DesignSparkRS/ESDK/hardware/PEA/DSPCB/ESDK-PEA (PCB - Plot Report).htm

## Plot Report

Report Written: | Tuesday, October 19, 2021
Project Path: | C:\Users\Callum\Google Drive\ABOPShared\Customer\RS\Projects\Team\Air Quality Sensor Dev Platform\Hardware\PMOD Transition Board\DSPCB Project\PMOD Transition Board.prj
Design Path: | C:\Users\Callum\Google Drive\ABOPShared\Customer\RS\Projects\Team\Air Quality Sensor Dev Platform\Hardware\PMOD Transition Board\DSPCB Project\ESDK-PEA.pcb
Design Title:
Created: | 10/08/2021 11:33:29
Last Saved: | 04/10/2021 16:04:47
Editing Time: | 2646 min
Units: | mm (precision 3)

## Device Settings

### Gerber Settings

Leading zero suppression.
G01 assumed throughout.
Line termination <*> .
3.5 format absolute inches.
Format commands defined in Gerber file.
Aperture table defined in Gerber file.
Hardware arcs allowed.

### Drill Settings

Excellon Format 2
Format 3.5 absolute in mm.
Zero suppression Leading

## Plots Output

### Gerber Output

C:\Users\Callum\Google Drive\ABOPShared\Customer\RS\Projects\Team\Air Quality Sensor Dev Platform\Hardware\PMOD Transition Board\DSPCB Project\Outputs\ESDK-PEA - Top Silkscreen.gbr

Layers:
Top Silkscreen

D-Code | Shape (thou)
D106 | Round 5.00
D107 | Round 3.94
D108 | Round 7.87
D109 | Round 10.00

### Gerber Output

C:\Users\Callum\Google Drive\ABOPShared\Customer\RS\Projects\Team\Air Quality Sensor Dev Platform\Hardware\PMOD Transition Board\DSPCB Project\Outputs\ESDK-PEA - Top Copper.gbr

Layers:
Top Copper

D-Code | Shape (thou)
D106 | Round 5.00
D108 | Round 7.87
D109 | Round 10.00
D110 | Round 25.00
D111 | Round 9.84
D112 | Round 35.43
D113 | Round 19.69
D114 | Round 15.00
D115 | Round 61.02
D116 | Rectangle 31.50 X 51.18 Rotation 90
D117 | Rectangle 82.68 X 118.11 Rotation 90
D118 | Round 55.12
D119 | Rectangle 39.37 X 42.91
D120 | Rectangle 39.37 X 42.91 Rotation 90

### Gerber Output

C:\Users\Callum\Google Drive\ABOPShared\Customer\RS\Projects\Team\Air Quality Sensor Dev Platform\Hardware\PMOD Transition Board\DSPCB Project\Outputs\ESDK-PEA - Top Copper (Resist).gbr

Layers:
Top Copper

D-Code | Shape (thou)
D12 | Round 135.98
D13 | Round 71.02
D17 | Rectangle 49.37 X 52.91 Rotation 90
D18 | Rectangle 49.37 X 52.91
D26 | Rectangle 41.50 X 61.18 Rotation 90
D27 | Rectangle 92.68 X 128.11 Rotation 90
D121 | Round 65.12

### Gerber Output

C:\Users\Callum\Google Drive\ABOPShared\Customer\RS\Projects\Team\Air Quality Sensor Dev Platform\Hardware\PMOD Transition Board\DSPCB Project\Outputs\ESDK-PEA - Top Paste.gbr

Layers:
Top Paste

D-Code | Shape (thou)
D83 | Rectangle 35.43 X 38.98 Rotation 90
D84 | Rectangle 35.43 X 38.98
D94 | Rectangle 28.35 X 48.03 Rotation 90
D95 | Rectangle 74.41 X 109.84 Rotation 90

### Gerber Output

C:\Users\Callum\Google Drive\ABOPShared\Customer\RS\Projects\Team\Air Quality Sensor Dev Platform\Hardware\PMOD Transition Board\DSPCB Project\Outputs\ESDK-PEA - Bottom Copper.gbr

Layers:
Bottom Copper

D-Code | Shape (thou)
D106 | Round 5.00
D108 | Round 7.87
D109 | Round 10.00
D110 | Round 25.00
D111 | Round 9.84
D112 | Round 35.43
D115 | Round 61.02
D118 | Round 55.12

### Gerber Output

C:\Users\Callum\Google Drive\ABOPShared\Customer\RS\Projects\Team\Air Quality Sensor Dev Platform\Hardware\PMOD Transition Board\DSPCB Project\Outputs\ESDK-PEA - Bottom Resist.gbr

Layers:
Bottom Resist

D-Code | Shape (thou)
D122 | Round 41.43
D123 | Round 131.98
D124 | Round 67.02
D125 | Round 61.12

### NC Drill Output

C:\Users\Callum\Google Drive\ABOPShared\Customer\RS\Projects\Team\Air Quality Sensor Dev Platform\Hardware\PMOD Transition Board\DSPCB Project\Outputs\ESDK-PEA - NC Drill Data - [Through Hole].drl

Output:

Plated Round Drill Holes

Plated Slots

Tool | Size | Count | ID
T001 | 0.01969 inches | 19 | A
T002 | 0.03150 inches | 4 | J
T003 | 0.04094 inches | 12 | G
Total | | 35

C:\Users\Callum\Google Drive\ABOPShared\Customer\RS\Projects\Team\Air Quality Sensor Dev Platform\Hardware\PMOD Transition Board\DSPCB Project\Outputs\ESDK-PEA - NC Drill Data - [Through Hole] (Unplated).drl

Output:

Unplated Round Drill Holes

Unplated Slots

Tool | Size | Count | ID
T001 | 0.12598 inches | 2 | F
Total | | 2

### Gerber Output

C:\Users\Callum\Google Drive\ABOPShared\Customer\RS\Projects\Team\Air Quality Sensor Dev Platform\Hardware\PMOD Transition Board\DSPCB Project\Outputs\ESDK-PEA - Drill Ident Drawing - [Through Hole].gbr

Layers:
[Through Hole]

### Drill Ident Drawing

Drill | Plated | Size | Shape | ID
20 | Y | 100 | Round | A
126 | | 100 | Round | F
41 | Y | 100 | Round | G
31 | Y | 100 | Round | J

D-Code | Shape (thou)
D105 | Round 100.00
D106 | Round 5.00

### Gerber Output

C:\Users\Callum\Google Drive\ABOPShared\Customer\RS\Projects\Team\Air Quality Sensor Dev Platform\Hardware\PMOD Transition Board\DSPCB Project\Outputs\ESDK-PEA - Outline.gbr

Layers:
Board Outlines

D-Code | Shape (thou)
D106 | Round 5.00
