DesignSparkRS/ESDK/hardware/PM2/DSPCB/ESDK-PM2 (AB_BOM_Template).csv

Names | Value | Quantity | Manufacturer | Manufacturer Part Number | Component
CONN1 |  | 1 |  |  | SolderBridge_0603_NC
J1 |  | 1 | SAMTEC | SSW-106-02-G-D-RA | SSW-106-02-G-D-RA
J2 |  | 1 | SAMTEC | TSW-106-08-G-D-RA | TSW-106-08-G-D-RA
J3 |  | 1 | JST (JAPAN SOLDERLESS TERMINALS) | B5B-ZR (LF)(SN) | B5B-ZR__LF__SN_
LED1 |  | 1 | Kingbright | KPA-3010YC | KPA-3010YC
M1 |  | 1 | Sensirion | SPS30 | SPS30
R1 | 330R | 1 | TE Connectivity | CRG0603F330R | Resistor
Sub-total: |  | 7
