DesignSparkRS/ESDK/hardware/PM2/DSPCB/SPS30 Module (Component Positions CSV).csv

Name | Component | Side | Place X | Place Y | Rotation
J3 | B5B-ZR__LF__SN_ | Top | 516.050 | 520.700 | 90.00
LOGO2 | Designspark_Logo | Top | 500.000 | 517.500 | 0.00
LED1 | KPA-3010YC | Top | 500.000 | 531.200 | 0.00
R1 | Resistor | Top | 493.600 | 528.100 | 180.00
LOGO1 | RS_Logo | Top | 500.105 | 524.030 | 0.00
CONN1 | SolderBridge_0603_NC | Top | 506.300 | 529.700 | 180.00
M1 | SPS30 | Top | 502.550 | 491.600 | 0.00
J1 | SSW-106-02-G-D-RA | Top | 527.960 | 500.000 | 90.00
J2 | TSW-106-08-G-D-RA | Top | 477.500 | 500.000 | 90.00
