DesignSparkRS/ESDK/hardware/THV/DSPCB/Outputs/Schematic.pdf

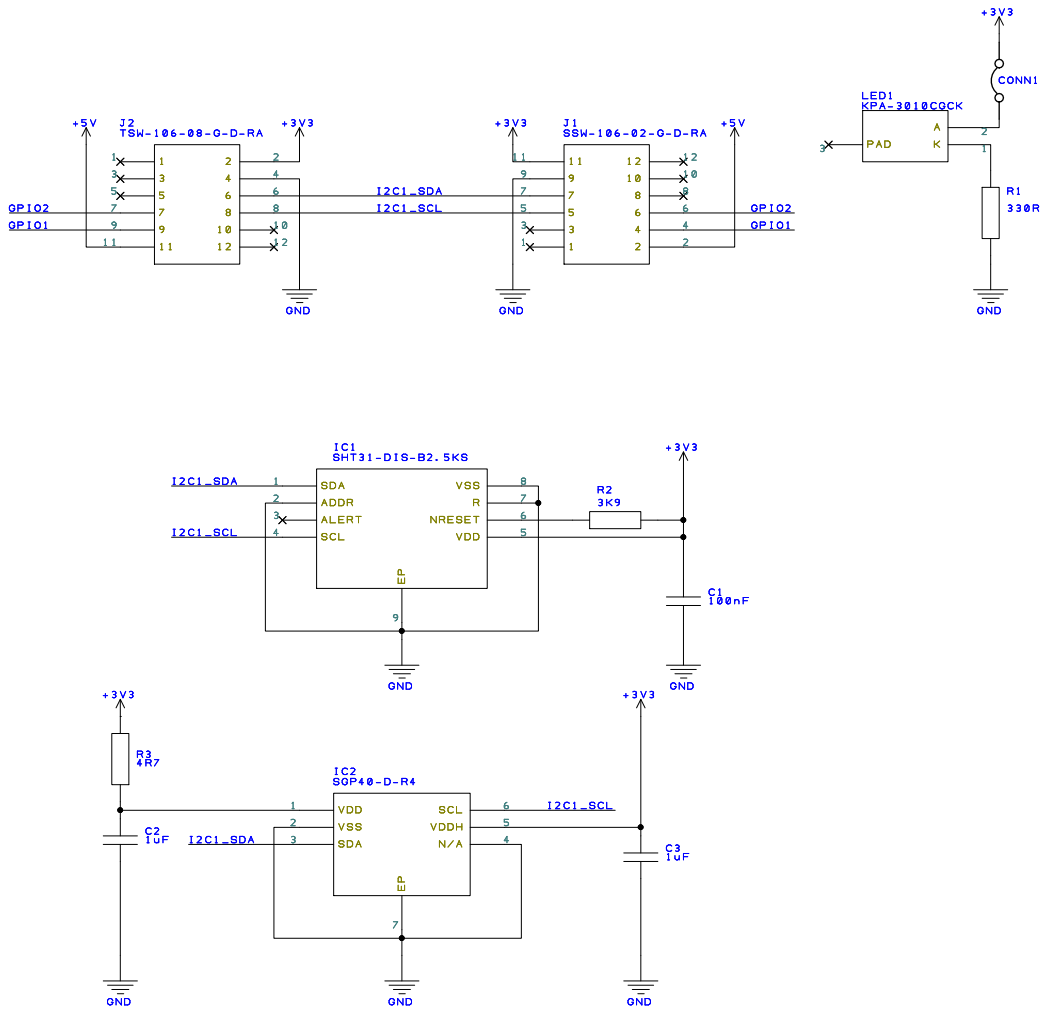
[picture p53: page 1]
